andrearante12/ImitationArm/robotic_arm_model/final/links/link9.SLDASM

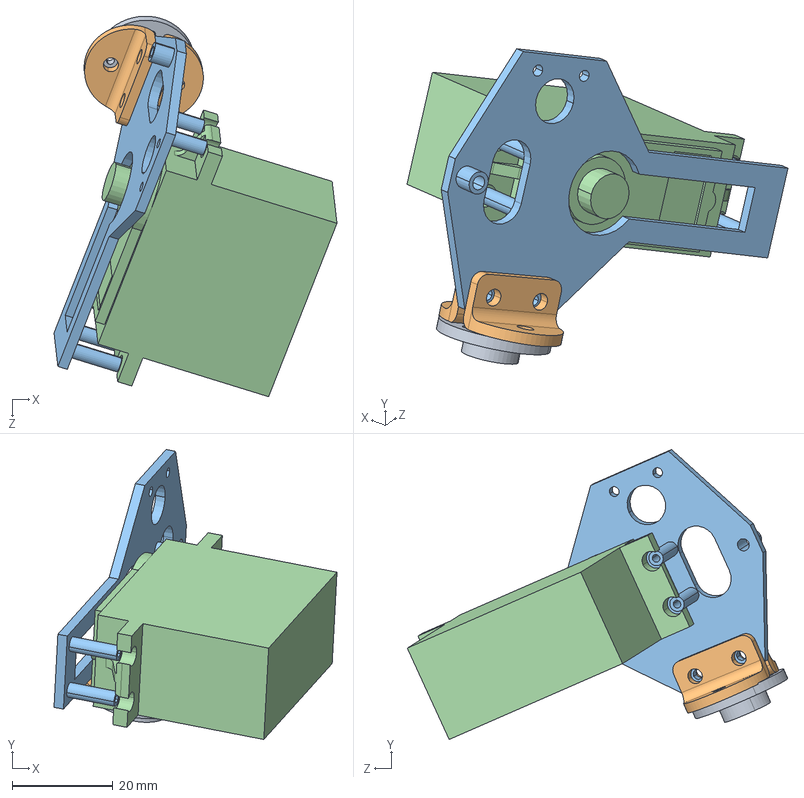
[picture p12: CAD file, 2025-12-21]
robotic_arm_model/final/links/link9.SLDASM
56.2 x 57.6 x 75.6 mm
simplified_servo
end_effector_base
end_effector_attachment x 2
servo_bearing
