andrearante12/ImitationArm/robotic_arm_model/final/links/link7.SLDASM

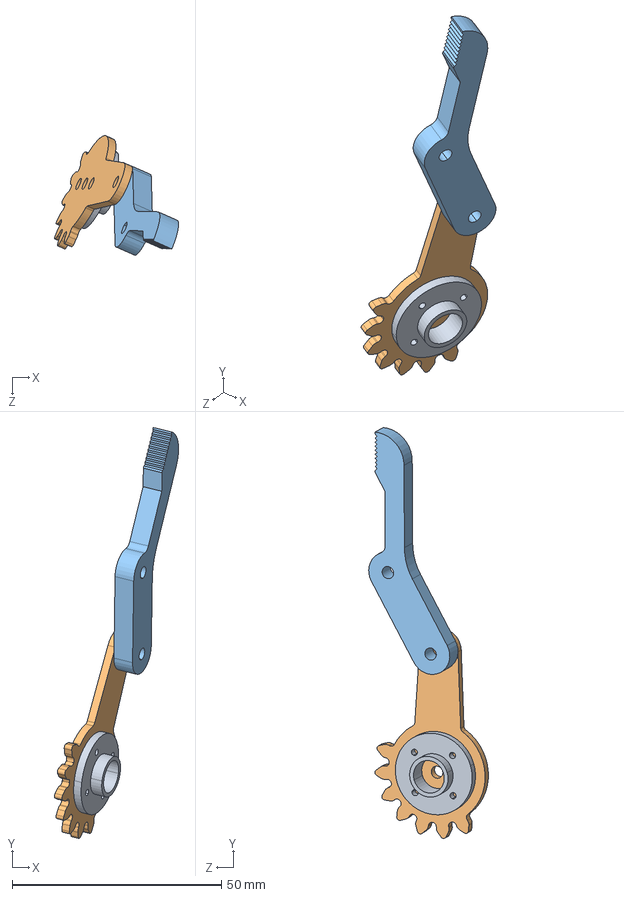
[picture p13: CAD file, 2025-12-21]
robotic_arm_model/final/links/link7.SLDASM
29.7 x 98.3 x 28.6 mm
end_effector_claw
end_effector_gear
servo_bearing
