andrearante12/ImitationArm/robotic_arm_model/final/links/link5.SLDASM

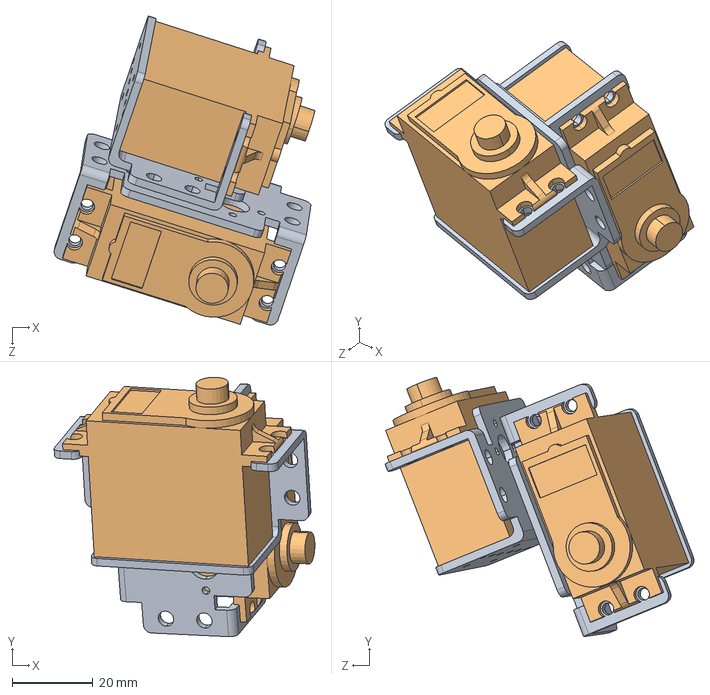
[picture p14: CAD file, 2025-12-21]
robotic_arm_model/final/links/link5.SLDASM
64.4 x 64.1 x 76.3 mm
simplified_servo x 2
servo_holder x 2
