andrearante12/ImitationArm/robotic_arm_model/final/links/link10.SLDASM

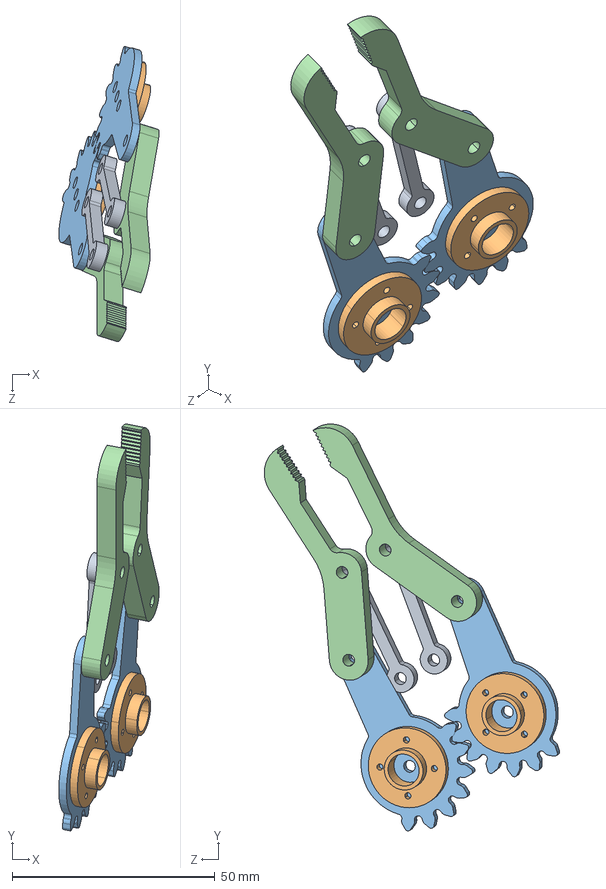
[picture p15: CAD file, 2025-12-21]
robotic_arm_model/final/links/link10.SLDASM
24.7 x 100.3 x 72.8 mm
end_effector_claw x 2
end_effector_gear x 2
servo_bearing x 2
end_effector_support_beam x 2
