andrearante12/ImitationArm/robotic_arm_model/final/end_effector_gear.SLDPRT

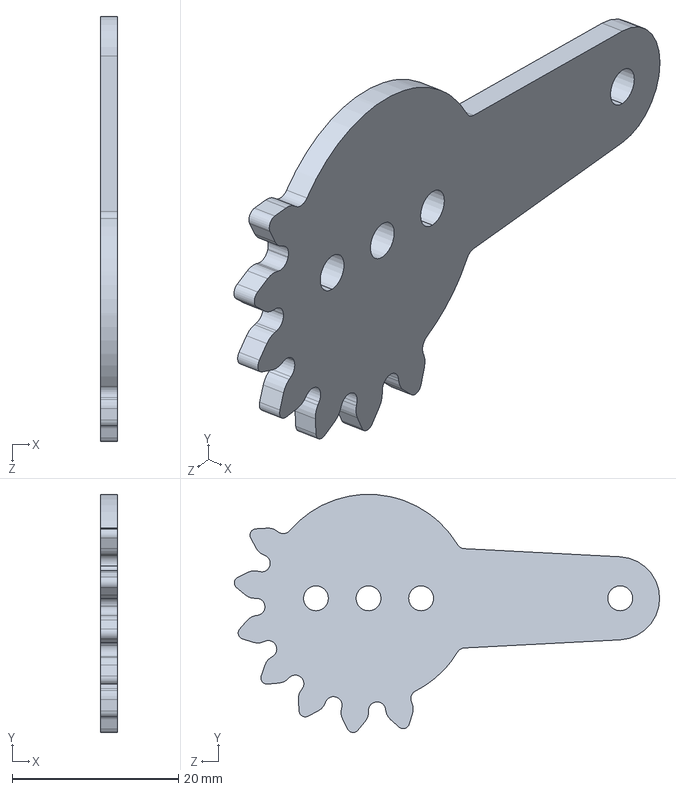
[picture p21: CAD file, 2025-12-21]
robotic_arm_model/final/end_effector_gear.SLDPRT
2.00 x 28.6 x 51.1 mm
