andrearante12/ImitationArm/robotic_arm_model/robotic_arm_model_v2/meshes/Link_4.STL

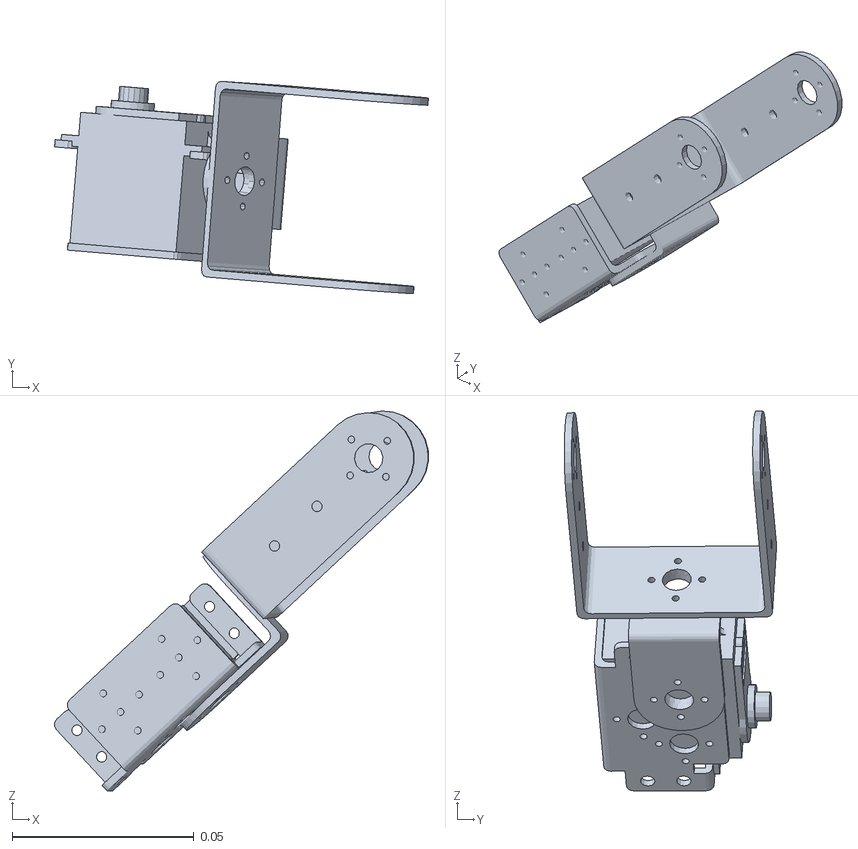
[picture p22: CAD file, 2025-12-22]
robotic_arm_model/robotic_arm_model_v2/meshes/Link_4.STL
0.103 x 0.0584 x 0.105
