andrearante12/ImitationArm/robotic_arm_model/final/end_effector_attachment.SLDPRT

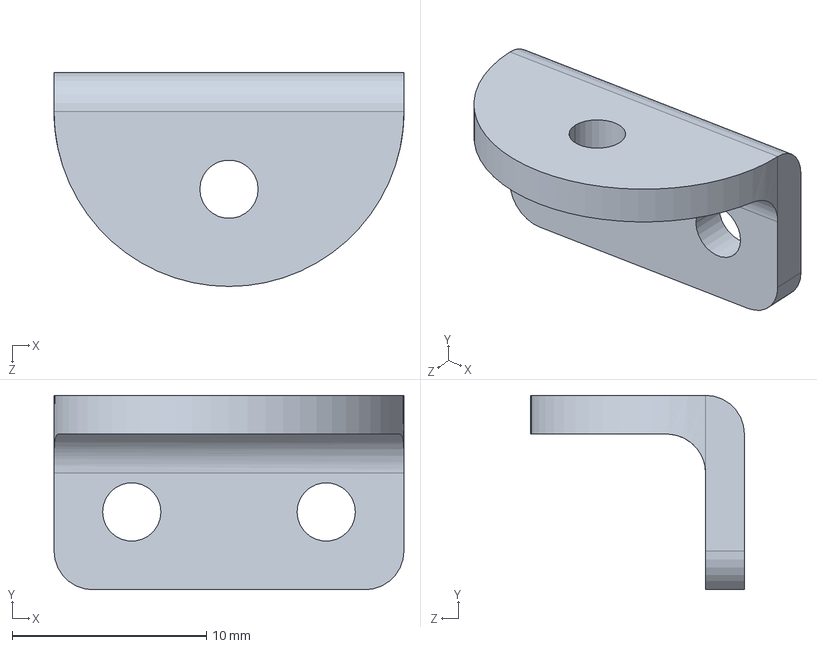
[picture p23: CAD file, 2025-12-21]
robotic_arm_model/final/end_effector_attachment.SLDPRT
18.0 x 10.0 x 11.0 mm
