andrearante12/ImitationArm/robotic_arm_model/robotic_arm_model_v2/meshes/Link_1.STL

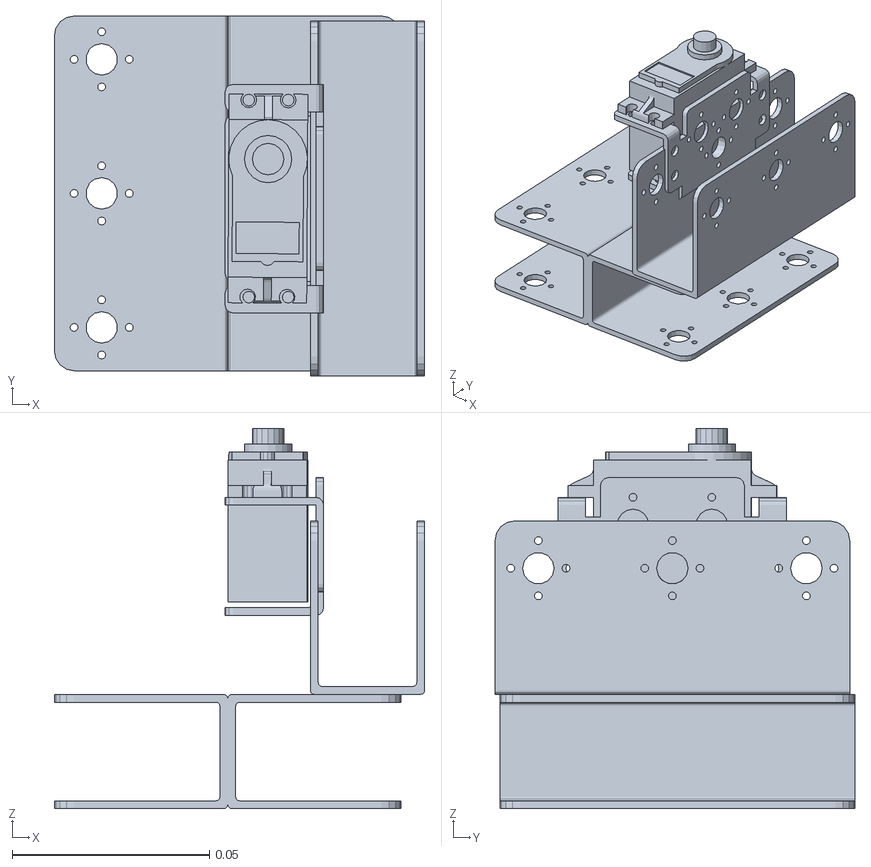
[picture p24: CAD file, 2025-12-22]
robotic_arm_model/robotic_arm_model_v2/meshes/Link_1.STL
0.0939 x 0.0913 x 0.0965
