andrearante12/ImitationArm/robotic_arm_model/final/end_effector_claw.SLDPRT

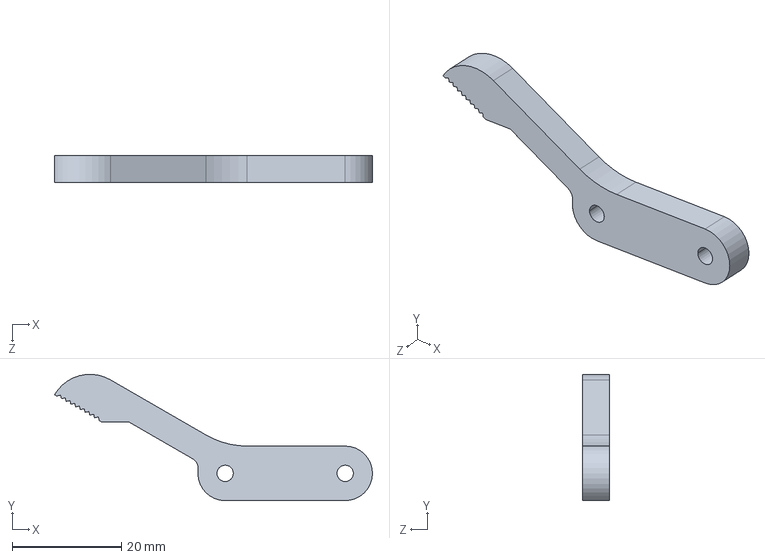
[picture p25: CAD file, 2025-12-21]
robotic_arm_model/final/end_effector_claw.SLDPRT
58.3 x 23.1 x 5.00 mm
