andrearante12/ImitationArm/robotic_arm_model/final/u_shaped_arm_bracket.SLDPRT

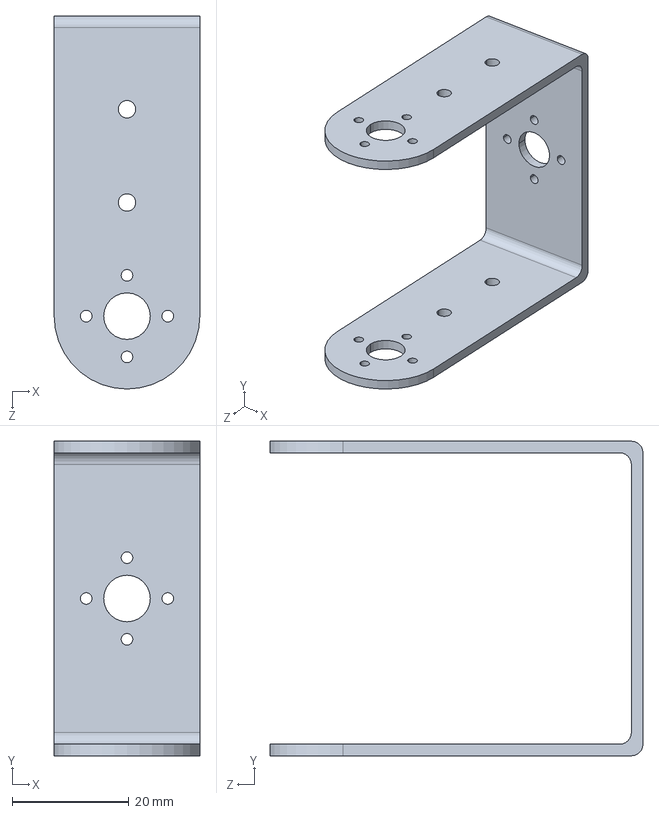
[picture p26: CAD file, 2025-12-21]
robotic_arm_model/final/u_shaped_arm_bracket.SLDPRT
25.0 x 54.0 x 64.0 mm
