andrearante12/ImitationArm/robotic_arm_model/final/end_effector_support_beam.SLDPRT

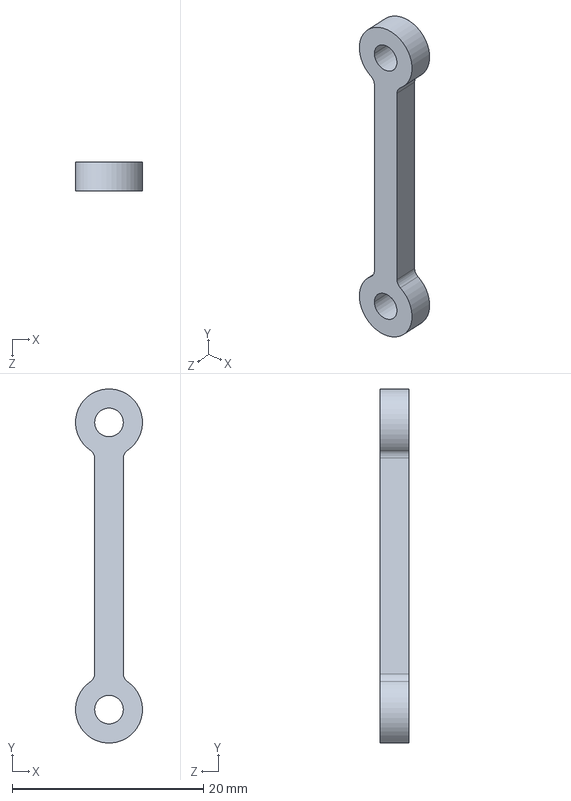
[picture p27: CAD file, 2025-12-21]
robotic_arm_model/final/end_effector_support_beam.SLDPRT
6.99 x 37.0 x 3.00 mm
