andrearante12/ImitationArm/robotic_arm_model/final/l_shaped_hinge.SLDPRT

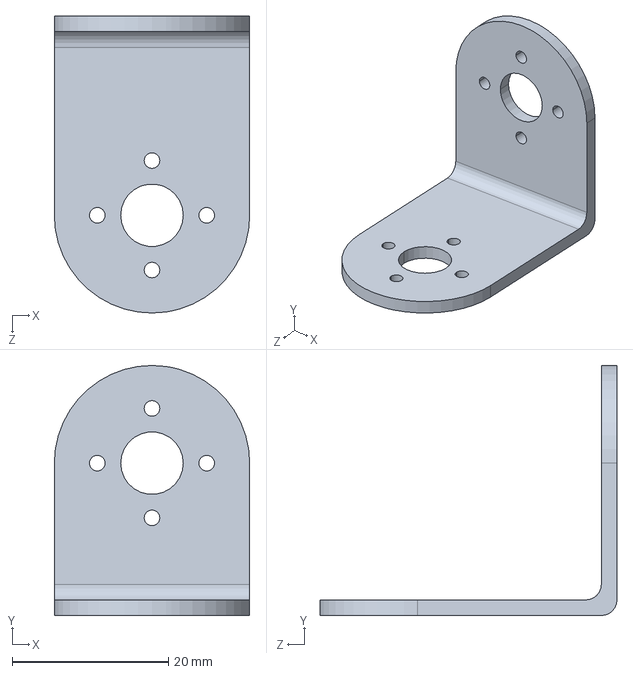
[picture p28: CAD file, 2025-12-21]
robotic_arm_model/final/l_shaped_hinge.SLDPRT
25.0 x 32.0 x 38.0 mm
