andrearante12/ImitationArm/robotic_arm_model/final/servo_holder.SLDPRT

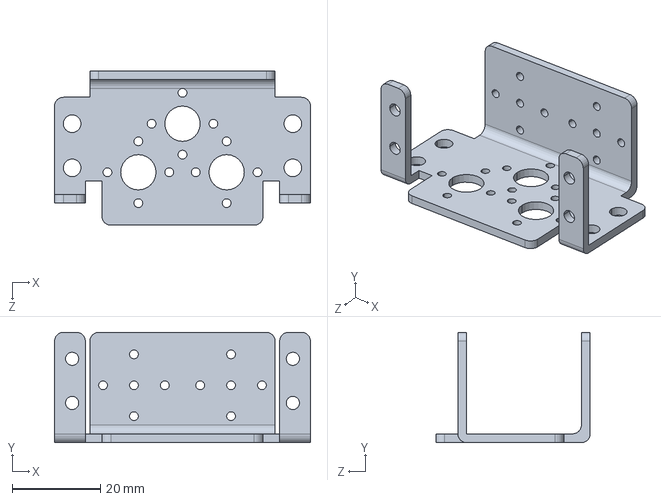
[picture p29: CAD file, 2025-12-21]
robotic_arm_model/final/servo_holder.SLDPRT
58.0 x 25.0 x 35.0 mm
