andrearante12/ImitationArm/robotic_arm_model/final/base_bracket.SLDPRT

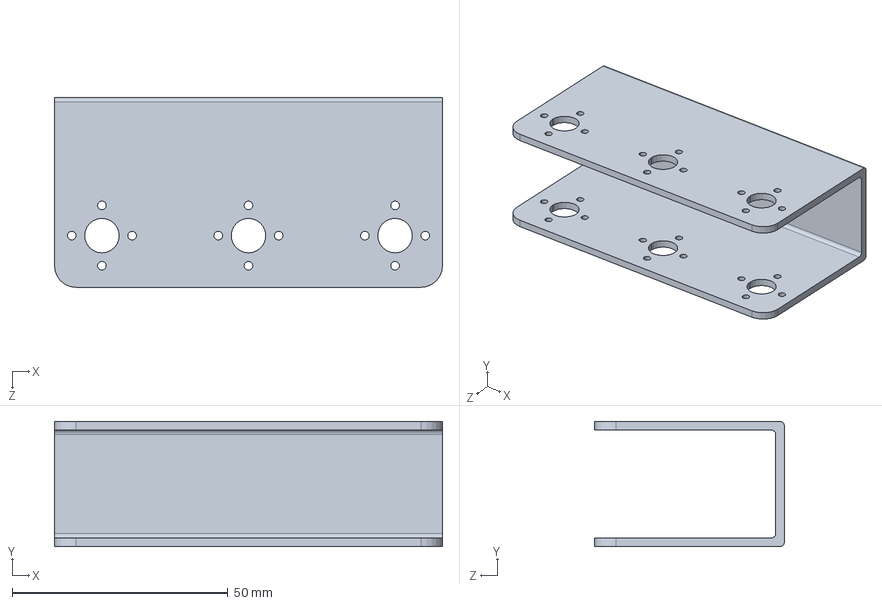
[picture p30: CAD file, 2025-12-21]
robotic_arm_model/final/base_bracket.SLDPRT
90.0 x 29.0 x 44.0 mm
