andrearante12/ImitationArm/robotic_arm_model/final/servo_bearing.SLDPRT

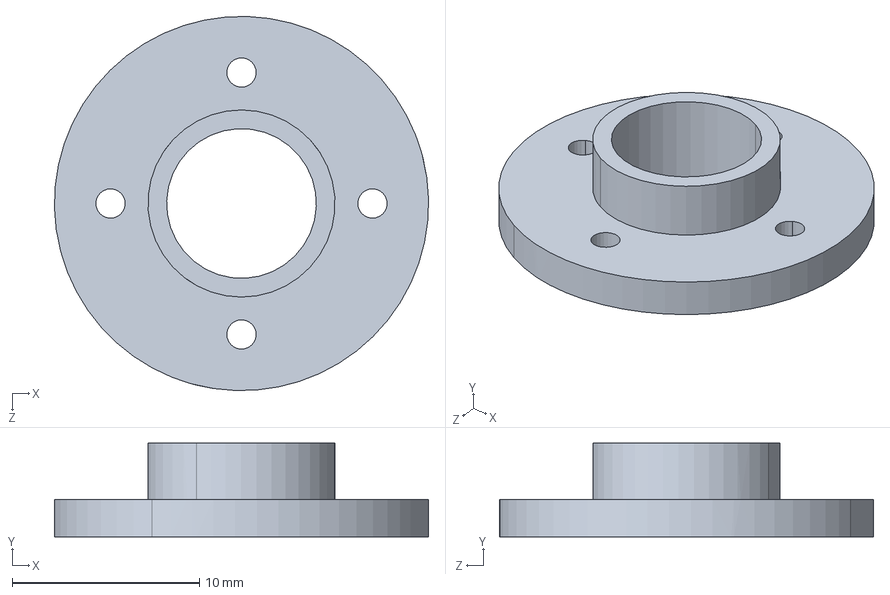
[picture p31: CAD file, 2025-12-21]
robotic_arm_model/final/servo_bearing.SLDPRT
20.0 x 5.00 x 20.0 mm
