andrearante12/ImitationArm/robotic_arm_model/final/end_effector_base.SLDPRT

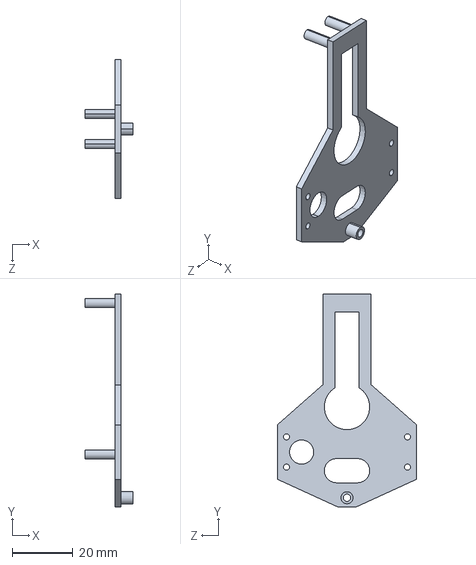
[picture p32: CAD file, 2025-12-21]
robotic_arm_model/final/end_effector_base.SLDPRT
16.0 x 70.4 x 46.0 mm
